dcpedit/adelheid-xt/bottom/bottom.kicad_sch

## KiCad design bottom/bottom.kicad_sch (2022-06-14)

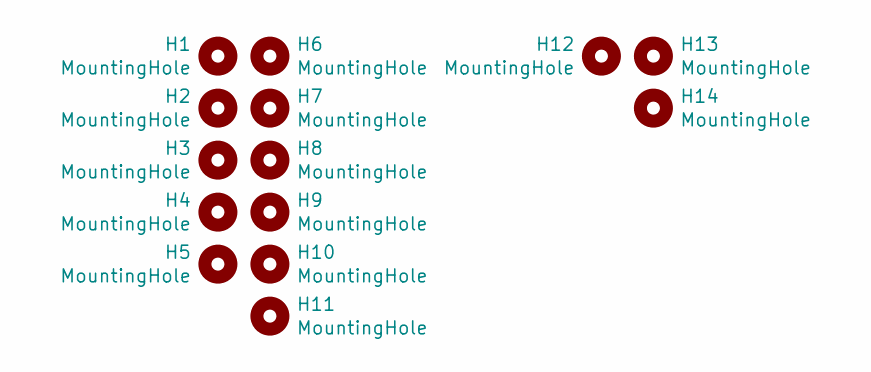
[picture p24: schematic bottom.kicad_sch]

Parts:
H1, H2, H3, H4, H5, H6, H7, H8, H9, H10, H11, H12, H13, H14: MountingHole; MountingHole_2.2mm_M2_Pad
