dcpedit/adelheid-xt/pcb/adelheid-xt.kicad_sch

## KiCad design pcb/adelheid-xt.kicad_sch (2022-06-14)

Schematic: adelheid-xt.kicad_sch

Parts:
D0, D1, D2, D3, D4, D5, D6, D7, D8, D9, D10, D11, D12, D13, D14, D15, D16, D17, D18, D19, D20, D21, D22, D23, D24, D25, D26, D27, D28, D29, D30, D31, D32, D33, D34, D35, D36, D37, D38, D39, D40, D41, D42, D43, D44, D45, D46, D47, D48, D49, D50, D51, D52, D53, D54, D55, D56, D57, D58, D59, D60, D61, D62, D63: BAV70; SOT-23_Handsoldering
H1, H2, H3, H4, H5, H6, H7, H8, H9, H10, H11: MountingHole; MountingHole_2.2mm_M2_Pad
J1: OLED; SSD1306_OLED
MX0000, MX0000.2, MX0001, MX0002, MX0003, MX0004, MX0005, MX0006, MX0007, MX0008, MX0009, MX0010, MX0011, MX0100, MX0101, MX0102, MX0103, MX0103.125, MX0104, MX0105, MX0106, MX0107, MX0108, MX0109, MX0110, MX0111, MX0111.125, MX0200, MX0201, MX0202, MX0203, MX0204, MX0206, MX0207, MX0208, MX0209, MX0210, MX0211, MX0211.225, MX0300, MX0301, MX0302, MX0303, MX0304, MX0306, MX0307, MX0308, MX0309, MX0310, MX0311, MX0400, MX0401, MX0404, MX0406, MX0407, MX0408, MX0409, MX0410, MX0411, MX0500, MX0501, MX0502, MX0503, MX0504, MX0506, MX0507, MX0508, MX0509, MX0510, MX0511, MX0600, MX0601, MX0602, MX0603, MX0604, MX0606, MX0607, MX0608, MX0609, MX0700, MX0701, MX0702, MX0703, MX0704, MX0706, MX0707, MX0708, MX0709, MX0801, MX0801.2, MX0802, MX0804, MX0805, MX0806, MX0807, MX0808, MX0811, MX0900, MX0901, MX0902, MX0904, MX0905, MX0906, MX0907, MX0908, MX0911, MX1000, MX1001, MX1002, MX1003, MX1004, MX1005, MX1005.2, MX1006, MX1007, MX1008, MX1009, MX1010, MX1011, MX1100, MX1101, MX1102, MX1103, MX1104, MX1105, MX1106, MX1107, MX1108, MX1109, MX1109.2, MX1110, MX1111, MX1111.2: MX-NoLED; MXOnly-1U-NoLED
SWR1: RotaryEncoder_Switch
U1: YAAJ_WeAct_BlackPill_Part_Like_SWD_Breakout; YAAJ_WeAct_BlackPill_SWD_2

Connections:
COL0: MX0000.1 (COL), MX0000.2.1 (COL), MX0001.1 (COL), MX0002.1 (COL), MX0003.1 (COL), MX0004.1 (COL), MX0005.1 (COL), MX0006.1 (COL), MX0007.1 (COL), MX0008.1 (COL), MX0009.1 (COL), MX0010.1 (COL), MX0011.1 (COL), U1.35 (PB1)
COL1: MX0100.1 (COL), MX0101.1 (COL), MX0102.1 (COL), MX0103.1 (COL), MX0103.125.1 (COL), MX0104.1 (COL), MX0105.1 (COL), MX0106.1 (COL), MX0107.1 (COL), MX0108.1 (COL), MX0109.1 (COL), MX0110.1 (COL), MX0111.1 (COL), MX0111.125.1 (COL), U1.34 (PB0)
COL2: MX0200.1 (COL), MX0201.1 (COL), MX0202.1 (COL), MX0203.1 (COL), MX0204.1 (COL), MX0206.1 (COL), MX0207.1 (COL), MX0208.1 (COL), MX0209.1 (COL), MX0210.1 (COL), MX0211.1 (COL), MX0211.225.1 (COL), U1.33 (PA7)
COL3: MX0300.1 (COL), MX0301.1 (COL), MX0302.1 (COL), MX0303.1 (COL), MX0304.1 (COL), MX0306.1 (COL), MX0307.1 (COL), MX0308.1 (COL), MX0309.1 (COL), MX0310.1 (COL), MX0311.1 (COL), U1.28 (PA2)
COL4: MX0400.1 (COL), MX0401.1 (COL), MX0404.1 (COL), MX0406.1 (COL), MX0407.1 (COL), MX0408.1 (COL), MX0409.1 (COL), MX0410.1 (COL), MX0411.1 (COL), U1.27 (PA1)
COL5: MX0500.1 (COL), MX0501.1 (COL), MX0502.1 (COL), MX0503.1 (COL), MX0504.1 (COL), MX0506.1 (COL), MX0507.1 (COL), MX0508.1 (COL), MX0509.1 (COL), MX0510.1 (COL), MX0511.1 (COL), U1.26 (PA0)
COL6: MX0600.1 (COL), MX0601.1 (COL), MX0602.1 (COL), MX0603.1 (COL), MX0604.1 (COL), MX0606.1 (COL), MX0607.1 (COL), MX0608.1 (COL), MX0609.1 (COL), U1.24 (PC15)
COL7: MX0700.1 (COL), MX0701.1 (COL), MX0702.1 (COL), MX0703.1 (COL), MX0704.1 (COL), MX0706.1 (COL), MX0707.1 (COL), MX0708.1 (COL), MX0709.1 (COL), SWR1.S1, U1.37 (PB10)
COL8: MX0801.1 (COL), MX0801.2.1 (COL), MX0802.1 (COL), MX0804.1 (COL), MX0805.1 (COL), MX0806.1 (COL), MX0807.1 (COL), MX0808.1 (COL), MX0811.1 (COL), U1.23 (PC14)
COL9: MX0900.1 (COL), MX0901.1 (COL), MX0902.1 (COL), MX0904.1 (COL), MX0905.1 (COL), MX0906.1 (COL), MX0907.1 (COL), MX0908.1 (COL), MX0911.1 (COL), U1.3 (PB14)
COL10: MX1000.1 (COL), MX1001.1 (COL), MX1002.1 (COL), MX1003.1 (COL), MX1004.1 (COL), MX1005.1 (COL), MX1005.2.1 (COL), MX1006.1 (COL), MX1007.1 (COL), MX1008.1 (COL), MX1009.1 (COL), MX1010.1 (COL), MX1011.1 (COL), U1.2 (PB13)
COL11: MX1100.1 (COL), MX1101.1 (COL), MX1102.1 (COL), MX1103.1 (COL), MX1104.1 (COL), MX1105.1 (COL), MX1106.1 (COL), MX1107.1 (COL), MX1108.1 (COL), MX1109.1 (COL), MX1109.2.1 (COL), MX1110.1 (COL), MX1111.1 (COL), MX1111.2.1 (COL), U1.1 (PB12)
GND: J1.1, SWR1.C, U1.19 (GND), U1.39 (GND), U1.41 (GND)
unnamed: D0.1 (A), MX0000.2 (ROW), MX0000.2.2 (ROW)
unnamed: D0.2 (A), MX0100.2 (ROW)
unnamed: D1.1 (A), MX0001.2 (ROW)
unnamed: D1.2 (A), MX0101.2 (ROW)
unnamed: D2.1 (A), MX0002.2 (ROW)
unnamed: D2.2 (A), MX0102.2 (ROW)
unnamed: D3.1 (A), MX0003.2 (ROW)
unnamed: D3.2 (A), MX0103.2 (ROW), MX0103.125.2 (ROW)
unnamed: D4.1 (A), MX0004.2 (ROW)
unnamed: D4.2 (A), MX0104.2 (ROW)
unnamed: D5.1 (A), MX0005.2 (ROW)
unnamed: D5.2 (A), MX0105.2 (ROW)
unnamed: D6.1 (A), MX0006.2 (ROW)
unnamed: D6.2 (A), MX0106.2 (ROW)
unnamed: D7.1 (A), MX0007.2 (ROW)
unnamed: D7.2 (A), MX0107.2 (ROW)
unnamed: D8.1 (A), MX0008.2 (ROW)
unnamed: D8.2 (A), MX0108.2 (ROW)
unnamed: D9.1 (A), MX0009.2 (ROW)
unnamed: D9.2 (A), MX0109.2 (ROW)
unnamed: D10.1 (A), MX0010.2 (ROW)
unnamed: D10.2 (A), MX0110.2 (ROW)
unnamed: D11.1 (A), MX0011.2 (ROW)
unnamed: D11.2 (A), MX0111.2 (ROW), MX0111.125.2 (ROW)
unnamed: D12.1 (A), MX0200.2 (ROW)
unnamed: D12.2 (A), MX0300.2 (ROW)
unnamed: D13.1 (A), MX0201.2 (ROW)
unnamed: D13.2 (A), MX0301.2 (ROW)
unnamed: D14.1 (A), MX0202.2 (ROW)
unnamed: D14.2 (A), MX0302.2 (ROW)
unnamed: D15.1 (A), MX0203.2 (ROW)
unnamed: D15.2 (A), MX0303.2 (ROW)
unnamed: D16.1 (A), MX0204.2 (ROW)
unnamed: D16.2 (A), MX0304.2 (ROW)
unnamed: D17.1 (A), MX0206.2 (ROW)
unnamed: D17.2 (A), MX0306.2 (ROW)
unnamed: D18.1 (A), MX0207.2 (ROW)
unnamed: D18.2 (A), MX0307.2 (ROW)
unnamed: D19.1 (A), MX0208.2 (ROW)
unnamed: D19.2 (A), MX0308.2 (ROW)
unnamed: D20.1 (A), MX0209.2 (ROW)
unnamed: D20.2 (A), MX0309.2 (ROW)
unnamed: D21.1 (A), MX0210.2 (ROW)
unnamed: D21.2 (A), MX0310.2 (ROW)
unnamed: D22.1 (A), MX0211.2 (ROW), MX0211.225.2 (ROW)
unnamed: D22.2 (A), MX0311.2 (ROW)
unnamed: D23.1 (A), MX0400.2 (ROW)
unnamed: D23.2 (A), MX0500.2 (ROW)
unnamed: D24.1 (A), MX0401.2 (ROW)
unnamed: D24.2 (A), MX0501.2 (ROW)
unnamed: D25.2 (A), MX0502.2 (ROW)
unnamed: D26.2 (A), MX0503.2 (ROW)
unnamed: D27.1 (A), MX0404.2 (ROW)
unnamed: D27.2 (A), MX0504.2 (ROW)
unnamed: D28.1 (A), MX0406.2 (ROW)
unnamed: D28.2 (A), MX0506.2 (ROW)
unnamed: D29.1 (A), MX0407.2 (ROW)
unnamed: D29.2 (A), MX0507.2 (ROW)
unnamed: D30.1 (A), MX0408.2 (ROW)
unnamed: D30.2 (A), MX0508.2 (ROW)
unnamed: D31.1 (A), MX0409.2 (ROW)
unnamed: D31.2 (A), MX0509.2 (ROW)
unnamed: D32.1 (A), MX0410.2 (ROW)
unnamed: D32.2 (A), MX0510.2 (ROW)
unnamed: D33.1 (A), MX0411.2 (ROW)
unnamed: D33.2 (A), MX0511.2 (ROW)
unnamed: D34.1 (A), MX0600.2 (ROW)
unnamed: D34.2 (A), MX0700.2 (ROW)
unnamed: D35.1 (A), MX0601.2 (ROW)
unnamed: D35.2 (A), MX0701.2 (ROW)
unnamed: D36.1 (A), MX0602.2 (ROW)
unnamed: D36.2 (A), MX0702.2 (ROW)
unnamed: D37.1 (A), MX0603.2 (ROW)
unnamed: D37.2 (A), MX0703.2 (ROW)
unnamed: D38.1 (A), MX0604.2 (ROW)
unnamed: D38.2 (A), MX0704.2 (ROW)
unnamed: D39.1 (A), MX0606.2 (ROW)
unnamed: D39.2 (A), MX0706.2 (ROW), SWR1.S2
unnamed: D40.1 (A), MX0607.2 (ROW)
unnamed: D40.2 (A), MX0707.2 (ROW)
unnamed: D41.1 (A), MX0608.2 (ROW)
unnamed: D41.2 (A), MX0708.2 (ROW)
unnamed: D42.1 (A), MX0609.2 (ROW)
unnamed: D42.2 (A), MX0709.2 (ROW)
unnamed: D43.2 (A), MX0900.2 (ROW)
unnamed: D44.1 (A), MX0801.2 (ROW), MX0801.2.2 (ROW)
unnamed: D44.2 (A), MX0901.2 (ROW)
unnamed: D45.1 (A), MX0802.2 (ROW)
unnamed: D45.2 (A), MX0902.2 (ROW)
unnamed: D46.1 (A), MX0804.2 (ROW)
unnamed: D46.2 (A), MX0904.2 (ROW)
unnamed: D47.1 (A), MX0805.2 (ROW)
unnamed: D47.2 (A), MX0905.2 (ROW)
unnamed: D48.1 (A), MX0806.2 (ROW)
unnamed: D48.2 (A), MX0906.2 (ROW)
unnamed: D49.1 (A), MX0807.2 (ROW)
unnamed: D49.2 (A), MX0907.2 (ROW)
unnamed: D50.1 (A), MX0808.2 (ROW)
unnamed: D50.2 (A), MX0908.2 (ROW)
unnamed: D51.1 (A), MX0811.2 (ROW)
unnamed: D51.2 (A), MX0911.2 (ROW)
unnamed: D52.1 (A), MX1000.2 (ROW)
unnamed: D52.2 (A), MX1100.2 (ROW)
unnamed: D53.1 (A), MX1001.2 (ROW)
unnamed: D53.2 (A), MX1101.2 (ROW)
unnamed: D54.1 (A), MX1002.2 (ROW)
unnamed: D54.2 (A), MX1102.2 (ROW)
unnamed: D55.1 (A), MX1003.2 (ROW)
unnamed: D55.2 (A), MX1103.2 (ROW)
unnamed: D56.1 (A), MX1004.2 (ROW)
unnamed: D56.2 (A), MX1104.2 (ROW)
unnamed: D57.1 (A), MX1005.2 (ROW), MX1005.2.2 (ROW)
unnamed: D57.2 (A), MX1105.2 (ROW)
unnamed: D58.1 (A), MX1006.2 (ROW)
unnamed: D58.2 (A), MX1106.2 (ROW)
unnamed: D59.1 (A), MX1007.2 (ROW)
unnamed: D59.2 (A), MX1107.2 (ROW)
unnamed: D60.1 (A), MX1008.2 (ROW)
unnamed: D60.2 (A), MX1108.2 (ROW)
unnamed: D61.1 (A), MX1009.2 (ROW)
unnamed: D61.2 (A), MX1109.2 (ROW), MX1109.2.2 (ROW)
unnamed: D62.1 (A), MX1010.2 (ROW)
unnamed: D62.2 (A), MX1110.2 (ROW)
unnamed: D63.1 (A), MX1011.2 (ROW)
unnamed: D63.2 (A), MX1111.2 (ROW), MX1111.2.2 (ROW)
RA: SWR1.A, U1.31 (PA5)
RB: SWR1.B, U1.32 (PA6)
ROW0: D0.3 (K), D12.3 (K), D23.3 (K), D34.3 (K), D43.3 (K), D52.3 (K), U1.30 (PA4)
ROW1: D1.3 (K), D13.3 (K), D24.3 (K), D35.3 (K), D44.3 (K), D53.3 (K), U1.43 (SWIO)
ROW2: D2.3 (K), D14.3 (K), D25.3 (K), D36.3 (K), D45.3 (K), D54.3 (K), U1.12 (PB4)
ROW3: D3.3 (K), D15.3 (K), D26.3 (K), D37.3 (K), D55.3 (K), U1.17 (PB9)
ROW4: D4.3 (K), D16.3 (K), D27.3 (K), D38.3 (K), D46.3 (K), D56.3 (K), U1.10 (PA15)
ROW5: D5.3 (K), D47.3 (K), D57.3 (K), U1.4 (PB15)
ROW6: D6.3 (K), D17.3 (K), D28.3 (K), D39.3 (K), D48.3 (K), D58.3 (K), U1.29 (PA3)
ROW7: D7.3 (K), D18.3 (K), D29.3 (K), D40.3 (K), D49.3 (K), D59.3 (K), U1.42 (SWCLK)
ROW8: D8.3 (K), D19.3 (K), D30.3 (K), D41.3 (K), D50.3 (K), D60.3 (K), U1.13 (PB5)
ROW9: D9.3 (K), D20.3 (K), D31.3 (K), D42.3 (K), D61.3 (K), U1.16 (PB8)
ROW10: D10.3 (K), D21.3 (K), D32.3 (K), D62.3 (K), U1.11 (PB3)
ROW11: D11.3 (K), D22.3 (K), D33.3 (K), D51.3 (K), D63.3 (K), U1.5 (PA8)
SCL: J1.3, U1.14 (PB6)
SDA: J1.4, U1.15 (PB7)
VCC: J1.2, U1.40 (5V)
